ghztomash/callisto-module/firmware/drum-synth/AudioSampleCclap.cpp

// Audio data converted from WAV file by wav2sketch

#include "AudioSampleCclap.h"

// Converted from cclap.wav, using 44100 Hz, 16 bit PCM encoding
const unsigned int AudioSampleCclap[8833] = {
0x810044E8,0x00000000,0x00000000,0x00000000,0x00000000,0x00000000,0x00000000,0x0000FFFF,
0xFFFEFFFF,0xFFF6FFFE,0x0069000E,0x02CA00FF,0x0DA0083B,0x0A0D0FD7,0x05D10537,0x05DA048E,
0xF759FCD4,0xF66FF671,0xF0BFF594,0xC32CE56E,0xCFE7B396,0xDFFFE4FB,0xCCBECF0B,0xC8C1CF38,
0xD81ED27F,0x039DF2EA,0x1CEF1B4C,0x2C9E1B59,0x5279362F,0x71856B8B,0x57C46E6F,0x24BE3C05,
0x1A42142B,0x0F2724F7,0xD678DE7E,0xC3BEC6D0,0xE34ECB49,0xAF9BE7E2,0xA4F7969C,0xCC65C53A,
0xBEFEC7BB,0xB5B2AECB,0x0A7DD034,0x49E424F3,0x3CA65B39,0x721D45F5,0x7FFF7D3C,0x771B7FE0,
0x60FC66C9,0x3D735072,0xF5ED191B,0xD8B1E832,0x99A3B6CB,0x824A938E,0x884F8643,0xAC258784,
0x1354DF76,0xEA980F6E,0xDB5BEC39,0xF09FDA6F,0x04E30404,0xED0BF010,0xD35FDD2D,0x8E3899D1,
0xCF1AA1AD,0x2CB2FA63,0x579239BD,0x779F6F91,0x779F7BAB,0x603E6209,0x708771D2,0x3269599A,
0x43DB2C33,0x1F203123,0xD4B5F6FE,0xE397CC56,0xEEB0FC32,0xB519E76B,0x83D28D06,0x98E08B1D,
0xB228A036,0xC3EFBC7F,0x6CE41AC3,0x7A7C7D0A,0x09FA5221,0xC685DFB9,0xC8E8C79D,0x00CBD7E2,
0x314D371C,0xC418FA05,0x98859688,0x8F7292BB,0xA3498A4E,0xF5A3D082,0x0FC420BC,0x296F1A9F,
0x35BB1FC1,0x726E5D1C,0x5F417850,0xE385F978,0x2322128F,0xB9A50ABA,0xBD04AD18,0xFEF7C970,
0x66D64046,0x5C1A5F9D,0x10343BD2,0xF836FB74,0x14250467,0xFAAF0E3B,0x37870A34,0x2FB645A2,
0xF83C0BA6,0xC1B9E14E,0x912AA6BB,0xB2389C78,0x0429E052,0x347D1C0C,0x14442C00,0xEC55FBB0,
0xD577DDB8,0x21EAF607,0x49154262,0xF5A024CC,0xC550D4A6,0x081FDFD2,0x1FE5219C,0x0FC516D3,
0x050A03A3,0xF4DBF6CD,0xEF0FF3B7,0xD33CDD32,0xB074D06F,0xD1DAB9BE,0x0837F3A1,0x233512AF,
0x18752015,0x295B199A,0x3EB33078,0x23AE371D,0x25792089,0x3277330D,0x438F3A59,0x2C192ECB,
0x0DC620F9,0xECB1F9A2,0xD0A1D5FD,0xC890C527,0xC8FEC7EF,0xCC6CC572,0xD631D424,0xC9EBCB5A,
0xBA59C24E,0xDA3BC264,0x1508FAEF,0x2AD926C7,0x1CDD2624,0x143E15CE,0x36A82A17,0x2D293657,
0x08E11631,0x1E4B026E,0x37B42EE8,0x2C41390B,0x02471C53,0xC90BE561,0xC315C29B,0xC620C175,
0xD1B1CAAF,0xD10ED0D6,0xD7A8CE50,0xEE88E2D5,0x0964F93F,0x1D5809E4,0x28D42CB9,0x0A061E0F,
0xFC99FF52,0x16330BD6,0x16310FAE,0x2BBD2AF2,0x08FC1E9E,0x0473FAFF,0x13AA0839,0x076214DB,
0xF09904FC,0xFDF5ED66,0x035B0689,0xE42FF524,0xEA97E5D6,0xF30BECD8,0xDF28E859,0xCE33D09D,
0xF35EDF28,0xF350F637,0xF091ECD6,0x369D0C75,0x50154DE8,0x4B544FC5,0x373A447C,0x1009242E,
0xF885FB56,0xF148E8E7,0x14E40C26,0x05A70D7A,0xDDA0F808,0xE95EE2DE,0xF9C3EBCE,0x06D9F9A8,
0x08BA0811,0xE8FBF9BF,0xD0A5E076,0xC721C529,0xC7BCC7F3,0xDCA8D08A,0xEC42DF05,0x14D5FFEF,
0x541932B2,0x611E6013,0x4FD85A73,0x2C68341D,0x1FDF2C0F,0xFCC41398,0xF0D8E8D7,0xEE64F05E,
0xC78DDDEC,0xC48AB9B3,0xDA89D4F1,0xF3D3EB43,0xFA14F386,0xDEDBF36D,0xD0F8D6E1,0xDAFBDD31,
0xDCB7E2B0,0xE3FBD652,0x1487FA4F,0x448C33D8,0x2EDE3FBA,0xDCE105F2,0xE206CE4C,0x0568F6B7,
0x04A00E81,0x101B0ADC,0xFEF50648,0xF2BFF1EE,0xEFC4F125,0x11C601BC,0x35EC2890,0x709D4EAF,
0x7D33792F,0x7CF27E46,0x7BE77CD8,0x83FBDE75,0x026982E6,0x877D3CA7,0x865884C0,0x86D883EC,
0x86D08426,0x86A08AB8,0x9512934A,0xEED9A2A3,0x7A983627,0x7B057922,0x7AD87880,0x51266F11,
0x7BF26D04,0x21366A96,0x7A4673C1,0x79A577B6,0x527C6F1E,0x0B94FF2E,0xBD6AFEA8,0x435AC142,
0x76DA7A4A,0x76B97A69,0x76C37A6A,0x77177A61,0x761679A7,0x896BC234,0xB1E0AD79,0x93D8A700,
0xC22AACA5,0xAA9DB955,0x783A1D48,0x782377E4,0x76E97811,0x772F7871,0x76C8790C,0x764979AB,
0x304E7813,0xFD83CDCA,0x72B820BA,0x75B979F5,0x352C6473,0x162C1AB4,0x97A4F855,0x05D19896,
0x59165D9D,0xA227D25D,0xA0A6AB4E,0x5DADF549,0x78787742,0x152854C8,0x748A37A3,0x789975D4,
0x049752BD,0x78E953CA,0x78A676A6,0x785776EF,0x77A4771F,0x43B54977,0x176D382E,0x368F1D00,
0x10FE2135,0x69DF4CD0,0x38AB60C5,0x720755DE,0x77DF7648,0x776C7768,0x771777CA,0x540C7842,
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
};
