ghztomash/callisto-module/firmware/drum-synth/AudioSampleChat1.cpp

// Audio data converted from WAV file by wav2sketch

#include "AudioSampleChat1.h"

// Converted from chat1.wav, using 44100 Hz, 16 bit PCM encoding
const unsigned int AudioSampleChat1[8833] = {
0x810044E8,0xFFFF0001,0xFFFF0001,0x00000001,0x0003FFFF,0x0008FFFB,0x0027FFF5,0x0062FFB7,
0xFFBDFFCE,0xFFA5FD3F,0xFF720575,0x08D70556,0x07380674,0xE300F971,0x11CCF55C,0x06251241,
0xE1F1E32E,0xFC97F3D8,0x229821B8,0xF5462300,0xFBC0D2EC,0x07EFEC0A,0x06FB2626,0x2D90FCB6,
0x23671DFC,0xBE81FB95,0x1430DDD1,0x34F345A2,0xC65BFF5D,0xE6ACC791,0x3E69270B,0xE470FA6D,
0xD8E7FE9D,0x19F7F01F,0x0B0D3184,0x0FBA0278,0xE1FEF3AF,0xD878B7A9,0xDD4DB2AA,0x1A35155B,
0x03E83A13,0xDE0FE2AC,0xF6FAD71A,0x05102248,0x0DD80C1A,0x1F6B0799,0xE94CEADA,0x1B5D3042,
0xE1BF3894,0xE7A3A7C7,0x33D40931,0xEA0123C3,0xFC33D661,0x3B4913E5,0x42491FA0,0xCAFD1BBB,
0xECFC9ED2,0x561453B0,0xD69A35E8,0x02AED1FC,0xC7B3EF15,0x2332FE34,0x52B83019,0x8000F806,
0xD3889F14,0x485C4E74,0x8652A158,0x68672B6A,0xE12CB768,0x303A353D,0xAE0BE3DE,0xEEE3B3DB,
0x1BA5292D,0xF2A32134,0x4B7BE69C,0x22FB625E,0xA556EBFE,0x46A405EB,0xB1CDC5BA,0x6D863567,
0xCC6B1BC9,0x4B37E680,0xF778203B,0xCC691366,0xEF65B92B,0x4EC23A66,0xD70E25E8,0xBB7C8F34,
0x74B63526,0xD2963E80,0x16A5C713,0xB2C1F623,0x06CDD588,0xE46F0BE1,0x0E951A26,0xB4D5D1AA,
0x5CECE460,0x1E295F95,0xA1CADD4D,0xFA38A316,0x3EB72C01,0xD9AE19AC,0xECDCCDC3,0x18BBE9F8,
0x238174F4,0xDF4BF2C4,0xD11BB640,0xC772B9C1,0x517EFD3A,0xF3E1465F,0x7A7542D2,0xE1F24E08,
0x5566D9DE,0xCB0B3C55,0x00BDD283,0x2CFE47DF,0x38F8F11C,0xC4DF164B,0xD4DBA485,0x150C42E1,
0x3D3DFAA6,0xB8ECF167,0x2F210C8C,0x88D0C2F6,0xB0D78D03,0x113D215F,0x0423D4FD,0x4BE0651E,
0xB9D6C4E8,0xE54EF50E,0xE2FEDB09,0x7A6D47E1,0xF36C2BC4,0xE511C18C,0xFC62F3B9,0x399A0FDD,
0xF98E5C02,0x0F76AC7B,0xE36941C0,0x15582376,0x231928E0,0xD7A39B68,0xFDD019CA,0xE854C6F5,
0x7CB07015,0xD9246052,0xE3CACA41,0xEFAAD73E,0x0D2EC305,0xFED14BB7,0xF881B88A,0xE1F9FE28,
0xECB43570,0xE450A23A,0x63E235A4,0xEBF5289E,0x285625F4,0xACDBD9B8,0x3982EF85,0xF78E128B,
0x5EAD5763,0x8955D929,0x729AF7FB,0xDECE2D07,0x852D9AB9,0x31F3DC5A,0xE85AF624,0x3B6E4EF0,
0x027DC710,0x3BE964BA,0xAC1DC8E6,0xE35F1441,0x216BB24B,0x461365F6,0xF66209D1,0x819CA5DA,
0x2D83A71C,0xED4B695A,0x4511DB67,0x395F72C7,0xC39CA245,0x8AA9A712,0x3C4A0A67,0xEBC443FA,
0x08969EEC,0x93DF1C1C,0x5E80B239,0x1C757451,0x96F2BC85,0xAB999675,0x6188FAB4,0xD5F35173,
0xEBA1E1A3,0x0192BC4C,0xA896F528,0x613602D7,0x1E5544F2,0xCE000784,0x3A3CD6BC,0xB89127EF,
0x541EB371,0xFBC072B8,0x261CF0E1,0x134E52CA,0x2964C96E,0x36A06CC4,0xDAF99C00,0x46006693,
0xEE2A24A1,0x36F7F9ED,0x9ABCF2D8,0x5771DA3D,0xB18A6286,0x14A98D88,0xC2301ADA,0x38FDAEB4,
0x1BF27F37,0xB2A98A45,0x5EE944E9,0x97F8C35F,0x65D43C2D,0x8884E77A,0xDAA7B895,0x13ADD4B2,
0x2A866C76,0xCA9EA3E5,0x554A3B78,0xA057DA8C,0xF925DB9B,0x0CD3E8E8,0xDEF6119E,0xD3F5B7DF,
0xE7041A81,0x0041EC07,0x260DD9AD,0xE97D3279,0xD1FCE63C,0x6C1EED73,0xCE385F43,0xE9C2ABCB,
0x4FAE4062,0x9D55E147,0x0A0DF2DF,0x34581FA2,0x4BC0EBDA,0xD0914082,0xFE32A5CF,0xE1756B9B,
0x3469D172,0x17535969,0xD4DEB4E1,0x0E920595,0x1F20D896,0x01DC6997,0xDF548881,0x0690411A,
0x2D7B2FEC,0xE8FA267A,0x2375BE65,0x0C734A30,0xDBB9A8CF,0x78616173,0xC07A1840,0x113CF626,
0x92B8D2AC,0x2E52E95F,0xCDEFE0FC,0x5AD1232E,0xD80E3A38,0x2778E659,0x9F27ED46,0x661EC7E5,
0x11D8550C,0xA9AAC936,0x10100E23,0x36B5F1C5,0xB3FC251C,0x1923BCCA,0x36F96B14,0xC726C6E6,
0x1E82FB71,0xF9D4F942,0xC9DC1E82,0xFE239DD7,0x1BAEFB03,0xEC3A4A67,0x0E65EF10,0xFFA31024,
0xE6280BB8,0xC7FC8C08,0xFCDE1E9E,0x17F6C5A3,0xF92967CA,0x9C0B9640,0x4D93F37E,0x5B54610B,
0xDD6E1E30,0xB58D991D,0xD027F6C0,0x2E240F08,0x3A7F37E7,0xCB5DFB79,0x2863D308,0x5BC14FE7,
0xE2060CB5,0xB03FEFD9,0x2513F932,0x239FFF28,0x372D3B9F,0x3EF1236D,0xED892681,0xEF07EB08,
0xB06BC64B,0x700339E2,0x254E2C6C,0xAA211B05,0xECB69373,0xEF401C85,0x115EC393,0x5C1A7156,
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
};
