ghztomash/callisto-module/firmware/drum-synth/AudioSampleChat2.cpp

// Audio data converted from WAV file by wav2sketch

#include "AudioSampleChat2.h"

// Converted from chat2.wav, using 44100 Hz, 16 bit PCM encoding
const unsigned int AudioSampleChat2[8833] = {
0x810044DA,0x00000000,0x00000000,0x00000000,0x00000000,0x00000000,0x00000000,0x00000000,
0x00000000,0x00000000,0x00000000,0xFFFF0001,0x00050002,0x00100006,0x00220059,0x00ED0057,
0x01EF0091,0xFAA9FF7D,0x0094FB24,0x07D207D7,0xFA69024E,0xF78FF5BA,0x01F7FD11,0x04830091,
0x00C30913,0xFD7EFB93,0x0381049C,0xF6C4F9C5,0x076DFEDB,0xFD65FEDC,0x06CAFC9F,0x0B520898,
0xFC34069F,0xED0BEEDD,0xF948FC9D,0xF638F476,0x08990B49,0xFB3CF514,0x200E1160,0xF24C0437,
0xF6FAF004,0xE358E483,0x14DC07D4,0x03851799,0x04B40FDD,0x034004ED,0xDDACF804,0x0787D2AA,
0x195A27F8,0x08AC0DD5,0x0A9718DE,0xEF78FAD1,0x1EAF0708,0xECF21BBD,0xD42AB687,0x0DD61B6D,
0x3F3F33B4,0xE7F40341,0x4176F732,0x2E9F36E1,0xD93D1332,0x42BFF911,0x13835575,0x96E8AF25,
0xC6518C13,0x35052F3E,0xED681CDB,0x07CEBBA1,0x020447CD,0xFC150612,0xBE04D7C0,0x4811F3F7,
0x2D0FDE77,0x16B47BC0,0x9E72C6EC,0x2083E67A,0x16185311,0x880086CB,0x3DB2CBEE,0x7C347C2B,
0xCE284C38,0xB758940A,0x47F0E5ED,0xD47B5DD7,0x78E91F9A,0x892FD430,0x80008973,0x7337D9C6,
0x64B57C9A,0x839EB048,0x254CC562,0x161D1CD5,0xB9E1BBB9,0x8B52F273,0x6E86B47F,0xC5E46071,
0x8F6788A0,0x2D4ED543,0x5D2F72BC,0x8E7BEAAC,0x1191C1EE,0xEFBF019C,0x7872586C,0x452A60B6,
0xFE323323,0x21D2F10A,0x9BE34C68,0x397D97E2,0x618A2CC8,0x002C669D,0x35BA201E,0xF5B31BB4,
0xF723FED3,0xA18893FA,0xCFAB11E5,0x75484C71,0xE68B6D22,0x05058B5C,0x01AE1595,0x61D9F1E4,
0x979F372C,0x002FCF73,0xC1002A7E,0x25AAFA92,0x30ECF9A6,0xAE4E04AC,0x98B48CA3,0x76204297,
0x99550C08,0x65DD287C,0xC96B2D0C,0x66F94C4C,0x8E6DC963,0x6A67B50B,0x5FA26B6C,0xC3CAEBB8,
0xA23EA019,0xC466BB11,0x601523DD,0xC9E74289,0x1C68AF81,0xACFF0304,0xAAE1A3E8,0x969EB306,
0x6E3B11D8,0x71106C91,0x9CD52487,0x2209C147,0x1C57517D,0xC8D4D243,0x2CFB0055,0xEF1817EF,
0xBAFCDF22,0x1579BF4E,0x2A7836E6,0x09600079,0x8BEEC7B8,0x63C9BBAB,0x63217519,0x8C13B447,
0x465DC9E1,0xFECE50CA,0xFBDA1785,0x0D6EC943,0xCF4ED688,0x959DB4A5,0x91A7942C,0x6CF4152D,
0xB4EE4060,0x6C10DDDC,0x612B4A0E,0xD479267E,0x14D00B2F,0xCED0D90E,0xE6F5D26B,0x38FA0A45,
0xF167424E,0x191831FA,0xC2C9B143,0x509D1A24,0xDE4A21CC,0x945D9938,0x6C32F467,0xCB8C6511,
0xA1868EA1,0x70EF3467,0xD57E6626,0x402DD686,0x67A7517F,0x671769A0,0xB860DE4E,0x6E3A677B,
0x54AD6A8E,0x15166989,0x3294DEEA,0x5DEE5589,0x5449604D,0x92A8DD45,0x544ED843,0x57526BC3,
0x6C286D2A,0x5B9D6350,0xA1ABFB26,0xF798987C,0x6C596C8A,0x65EF6CDC,0x43226D09,0x06B50517,
0xE2B4AFD1,0x3FA85DE5,0x1B5E2B18,0xBCBDFC0E,0x440CB94D,0xD12227C6,0x3C23BCED,0x588B6C2B,
0xC99D5CC6,0xE355948A,0x6DFE61EC,0x453E6B3C,0x0D95EDFE,0x0CCF0DEA,0x6F594C16,0x50416996,
0x989114D1,0xC1AE8FBF,0x6DCD5C00,0x4D704822,0xC6A9FAF6,0x608C4240,0x30BF5E90,0xACDCC796,
0x964EC58B,0x549EB3D7,0x13C36CF8,0x64C7D137,0x1A0B6A24,0x9244E157,0x5855B6ED,0x695A6D41,
0x02086CE8,0xC561A77D,0x2BFC6D19,0x5741CD72,0x10F20A5B,0x24032DEF,0xD6A905F8,0x286DE79D,
0x6DF966ED,0xD32035DF,0x54B411F3,0xF2FB40D9,0xEDE04788,0xD68D93B5,0x6219337B,0xF579168A,
0x34D300D8,0xF3E3206C,0x93A8C486,0x4E63C7DD,0xEE2753A4,0x6557E355,0x1A5518E3,0xD2906584,
0x5D2009C4,0xDA2F2C45,0x5A41D841,0x2F44509B,0xA1082EF2,0x6B4EEEA7,0x5FFE6C06,0xAF87DA3A,
0xADD2D45C,0x01A49575,0x65C36BA1,0x9821B0FA,0x47CC31C7,0x413756E6,0x60246B31,0x204E1279,
0x30892D06,0xB1D4B663,0x476F0AAC,0xEA0B9892,0x098A6C93,0xDA41FF22,0x690D18E0,0x95AF145C,
0x2E38A3A6,0x67FD6B39,0x60FE5B17,0xBF3760CA,0x47949C8D,0x634B6EBC,0xB897CFCE,0xFD54A618,
0x2D696E37,0x1D6CCDF5,0x1BB3423C,0xE1B8B60F,0x1F853F69,0xEBA59A88,0x36BA692F,0xACF0DACE,
0x078A4AAF,0x43542427,0x302FC04A,0xF55169D5,0xFB9EEE29,0x5652E033,0x984725C3,0x049E9A55,
0x570D6B76,0x632167D8,0xA092ACE0,0xE161ACD3,0x0AC9FA2C,0x5D6130B7,0x34465D5F,0x5CA9359C,
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
};
