ghztomash/callisto-module/firmware/drum-synth/AudioSampleCkick.cpp

// Audio data converted from WAV file by wav2sketch

#include "AudioSampleCkick.h"

// Converted from ckick.wav, using 44100 Hz, 16 bit PCM encoding
const unsigned int AudioSampleCkick[13249] = {
0x8100675C,0x000800BD,0x08BD039F,0x0F000C42,0x141E1187,0x15711595,0x16AB15FE,0x1448156E,
0x14DF13B8,0x18BD1776,0x19E818F8,0x225F1B40,0x39482D2E,0x4CD543CC,0x61B9576D,0x75966C75,
0x7D9A7B44,0x7F057EA5,0x7F4C7F38,0x7F067F39,0x7E687EBD,0x7DA37E08,0x7CD37D3A,0x7C0C7C6D,
0x7B587BAF,0x7AB97B04,0x7A307A71,0x793479EE,0x78237885,0x7639778A,0x6F06736A,0x64A869FA,
0x57235DED,0x4AA1517C,0x3B094326,0x2A4A3313,0x16A31FD3,0x02B70D48,0xEB90F739,0xD86AE18B,
0xCA54D092,0xBDB7C3EB,0xACB1B64C,0x9ED6A478,0x96489A43,0x8DF191F6,0x89838B08,0x882788AB,
0x87E487F2,0x886E882C,0x88E188AA,0x893E8911,0x89898965,0x89C689A9,0x89F789DF,0x8A208A0C,
0x8A448A33,0x8A638A54,0x8A7E8A71,0x8A968A8A,0x8AAB8AA1,0x8ABF8AB5,0x8AD08AC8,0x8AE08AD8,
0x8AEF8AE8,0x8AFC8AF5,0x8B088B02,0x8B138B0E,0x8B1D8B18,0x8B278B22,0x8B308B2B,0x8B388B34,
0x8B3F8B3B,0x8B478B42,0x8B4E8B48,0x8D478BBE,0x93288FC2,0x9C7A975D,0xAAC1A2E0,0xBE86B457,
0xD6B4CA68,0xEC8CE215,0x01A8F76F,0x172F0B9F,0x2F0B230D,0x462E3B47,0x59084FCC,0x672460E7,
0x6ECC6BB4,0x7346716A,0x74B47448,0x74B974BD,0x74B174B5,0x74A974AD,0x74A274A6,0x749C749F,
0x74967499,0x74907493,0x748B748E,0x74867489,0x74827484,0x747E7480,0x747A747C,0x74777479,
0x74747475,0x74717472,0x746E746F,0x746C746D,0x7469746B,0x74677468,0x74657466,0x74647465,
0x74627463,0x74617462,0x74607460,0x745F745F,0x745E745E,0x745D745D,0x745C745D,0x745C745C,
0x745B745B,0x745B745B,0x745B745B,0x745A745B,0x745A745A,0x745A745A,0x745A745B,0x745A745B,
0x745A745B,0x745B745C,0x745B745D,0x7435745D,0x70C8730E,0x696B6D97,0x5C57637B,0x4A905406,
0x35C8403F,0x22912C75,0x0E101828,0xF95C041F,0xE381EDE4,0xD14DDA28,0xBC35C6A1,0xAD42B415,
0xA004A666,0x967E9AAC,0x900492CC,0x8CA98E11,0x8BAB8BE9,0x8BC48BB8,0x8BDE8BD3,0x8BF68BEB,
0x8C0A8C00,0x8C1D8C14,0x8C2E8C25,0x8C3D8C36,0x8C4B8C44,0x8C588C52,0x8C648C5E,0x8C6E8C69,
0x8C788C73,0x8C818C7D,0x8C8A8C86,0x8C928C8E,0x8C998C95,0x8C9F8C9C,0x8CA68CA3,0x8CAB8CA8,
0x8CB18CAE,0x8CB58CB3,0x8CBA8CB8,0x8CBE8CBC,0x8CC28CC0,0x8CC58CC4,0x8CC98CC7,0x8CCC8CCA,
0x8CCE8CCD,0x8CD18CD0,0x8CD38CD2,0x8CD58CD4,0x8CD78CD6,0x8CD98CD8,0x8CDA8CDA,0x8CDC8CDB,
0x8CDD8CDC,0x8CDE8CDD,0x8CDF8CDE,0x8D1E8CDF,0x8F848E02,0x94E591C1,0x9D4298E0,0xA858A23E,
0xB65AAEF9,0xC698BE42,0xD894CF7D,0xEC0BE244,0x0144F6C5,0x15410B89,0x27851E5B,0x36562F3B,
0x44213D40,0x51BE4B16,0x5BD4579C,0x64195FF4,0x6A4C678B,0x6EA56C81,0x71EF709D,0x731672AD,
0x73467344,0x73447344,0x73437343,0x73417342,0x73407341,0x733F7340,0x733E733F,0x733E733E,
0x733D733E,0x733D733D,0x733D733D,0x733C733D,0x733C733C,0x733C733C,0x733C733C,0x733D733D,
0x733D733D,0x733D733D,0x733E733D,0x733E733E,0x733F733E,0x733F733F,0x73407340,0x73417340,
0x73427341,0x73427342,0x73437343,0x73447344,0x73457345,0x73467346,0x73477347,0x73497348,
0x734A7349,0x734B734A,0x734C734C,0x734D734D,0x734F734E,0x7350734F,0x73517351,0x73537352,
0x73547354,0x73567355,0x73577357,0x73537359,0x72AF7327,0x708571BC,0x6CF76F03,0x673D6A43,
0x5FD363D1,0x57745BCE,0x4C6C523E,0x3DA045B4,0x2CF73526,0x1C4A24D8,0x099B1328,0xF617FFE0,
0xE3CAEC5E,0xD3EEDBEF,0xC3E0CBDA,0xB5FABCA2,0xAABEB021,0xA137A58E,0x991C9D0D,0x92D29594,
0x8F2590C2,0x8D3F8E06,0x8C9B8CC3,0x8CAC8CA3,0x8CBD8CB5,0x8CCD8CC5,0x8CDC8CD5,0x8CE98CE2,
0x8CF58CEF,0x8D008CFB,0x8D0B8D05,0x8D148D0F,0x8D1D8D18,0x8D258D21,0x8D2C8D28,0x8D338D30,
0x8D398D36,0x8D3F8D3C,0x8D458D42,0x8D4A8D47,0x8D4E8D4C,0x8D528D50,0x8D568D54,0x8D5A8D58,
0x8D5D8D5C,0x8D608D5F,0x8D638D62,0x8D668D65,0x8D688D67,0x8D6A8D69,0x8D6C8D6B,0x8D6E8D6D,
0x8D6F8D6F,0x8D718D70,0x8D728D71,0x8D738D73,0x8D748D74,0x8D758D74,0x8D758D75,0x8D768D76,
0x8D768D76,0x8D778D77,0x8D778D77,0x8D778D77,0x8D778D77,0x8D778D77,0x8D778D77,0x8D768D77,
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
};
