ghztomash/callisto-module/firmware/drum-synth/AudioSampleCsnare.cpp

// Audio data converted from WAV file by wav2sketch

#include "AudioSampleCsnare.h"

// Converted from csnare.wav, using 44100 Hz, 16 bit PCM encoding
const unsigned int AudioSampleCsnare[8833] = {
0x810044E8,0xF5ADF66B,0xF4C5F500,0xF5EBF451,0xFE8BF8FA,0x18CF0A17,0x3C2D2AEA,0x5B094BE9,
0x6F736771,0x72BA72DA,0x6C4C6FFD,0x6452682E,0x5D3E60B0,0x568C59C1,0x50A15397,0x4A464DF1,
0x43934731,0x37893DED,0x2BDC31CB,0x229B26B4,0x1B981F4E,0x142617A9,0x0CDF1060,0x05170910,
0xFD58013A,0xF5D5F977,0xEF19F2A5,0xE893EBB1,0xE310E5BC,0xDD00E00A,0xD7CCDA2A,0xD2A3D558,
0xCE7AD06D,0xCADACCC8,0xC6EFC8A0,0xC476C527,0xC27DC3AA,0xB63BBF07,0x95BFAC86,0x8000830D,
0x811C8031,0x828681B1,0x83E9832B,0x85288485,0x863F85B5,0x872D86BA,0x87F68795,0x88CE884E,
0x8B3E89CA,0x8F8A8D27,0x9580925D,0x9CC69900,0xA4DBA0A2,0xAEBAA9B4,0xB97DB3FF,0xC52BBF25,
0xD1F1CB5A,0xE167D7F9,0xE69DE995,0x2D2AFA94,0x62374F33,0x74006F22,0x761C762D,0x75D97693,
0x74B47660,0x72B17567,0x729F754E,0x615372B3,0x39D75827,0x8892A429,0x91218B5A,0xBC47A9C5,
0xD6B4CCD8,0xEACEE258,0xFA65F3B4,0x062A0118,0x0F030C2C,0x124B109A,0x1A1A17CE,0x1D431B47,
0x23D92002,0x29AB25BB,0x2BF12AA5,0x343F2D78,0x43D63BC0,0x6D46654B,0x38815566,0x2DA82E23,
0x370D3101,0x3F473AE8,0x449C4127,0x48BE4573,0x4C0A48C2,0x58FA4B3B,0x5D6872C4,0x76457446,
0x7552747A,0x75CB740E,0x759674AE,0x756774D8,0x754074F4,0x75247504,0x75127508,0x74FA7504,
0x73F874AC,0x70B172B1,0x6A176DD2,0x5FF7657C,0x5253598F,0x41B04A55,0x2EE5387F,0x1AD424FA,
0x0646108E,0xF20AFC10,0xDED4E847,0xCD0FD5B9,0xBD23C4DF,0xAF70B5F7,0xA440A984,0x9B669F8B,
0x94C997D3,0x903D9246,0x8D948EB2,0x8C6F8CD5,0x8C7D8C60,0x8C9E8C92,0x8CAB8CA6,0x8CA38CB0,
0x8C9E8C96,0x8CB08CA8,0x8CC08CB9,0x8CD48CCA,0x8CEB8CE0,0x8CEE8CF5,0x8CE28CF4,0x8CCB8CFC,
0x8CA68D0A,0x8C718D30,0x8C2D8D6F,0x8BD28DB5,0x8B958E04,0x8BD78E65,0xCBC58FA6,0xA7F1B395,
0x8BDB8F31,0x8C218EA7,0x8C8C8E55,0x8D068E16,0x8D9E8DFD,0x8E028DF5,0x8E558DC6,0x8EA98D95,
0x8EF08D62,0x8F208D34,0x8F478D24,0x911A9093,0x7014460C,0x8F85D32A,0x8F5F8EC6,0x8F248EE6,
0x8F3A8EFB,0x94F29163,0xA0769A97,0xB08AA81E,0xCB18B5F4,0xD02AD13E,0xDB05D308,0xEE40E3E5,
0xFF25F530,0x0F2B044A,0x2F14128D,0x40354C1A,0x751E6AB6,0xEF785B2E,0x9C7F9233,0xDD88E740,
0x719F601B,0x733F46D8,0x9C5C39AC,0x99198DFE,0xD83AB864,0xE7D8E015,0xF39AEB53,0xFE89F880,
0x05620197,0x0A9B07CD,0x0ED70CAF,0x125010A2,0x154913CB,0x17FC16AB,0x1A58192D,0x1CC11B87,
0x1EAB1DA5,0x20921F74,0x2246213D,0x23C422C5,0x34652960,0x587144DC,0x70276E72,0x58686D54,
0x26A231D2,0x26742CEC,0xEE4B0EA9,0xE3F8DF53,0xFB46F028,0x0937032D,0x0F070E12,0x043D09F4,
0x01820187,0x03B60233,0x04240596,0x24B91420,0x04F91C16,0xE72BF09D,0xF0FCE72C,0x079AED5E,
0x19FA313C,0xD27FED4D,0xD3B3D05C,0xE83EE21B,0x4443EE9F,0x0FF64AF2,0xB031CCCC,0xB8F6B1A1,
0xC23DC02A,0xC264C29F,0xCE89C17D,0x0BCDE13A,0x700F6543,0x65C0702D,0x56215F54,0xEE051ACF,
0x64FC04B9,0x628C6E30,0x59A85A97,0x5AB35D80,0x52D7586E,0x465C4DBB,0x36583F2D,0x23042D3D,
0x0DAF18A9,0xF71B0285,0xE143EC0D,0xCCEBD6D7,0xBABAC35F,0xAC15B314,0xA08AA5F1,0x98649C07,
0x92FE955F,0x905A9146,0x9027902A,0x900A901A,0x90269008,0x908B9061,0x909E9092,0x9081909E,
0x9089907F,0x90989086,0x90429098,0x9030900C,0x9008902C,0x900F8FFA,0x90349040,0x90269011,
0x8FE29025,0x8F798F97,0x8F918F81,0x8FAA8F9A,0x8FE18FCD,0x8F9A8FCF,0x8F768F79,0x8F7A8F73,
0x8F968F85,0x8F7C8F8F,0x8F9F8F84,0x8FAF8FB2,0x8FE68FBE,0x8FE98FF2,0x8FBB8FEC,0x8F9B8F8C,
0x8F998F96,0x8FBE8FB4,0x8FD28FCF,0x8FBD8FB9,0x8F2C8F7F,0x8F8B8F62,0x8F898F85,0x8F4D8F67,
0x8F678F54,0x8F708F75,0x8F4E8F5F,0x8F428F4A,0x8F408F34,0x8F698F5B,0x8F698F6C,0x8F4B8F5C,
0x8F868F60,0x8FF68FCA,0x90B98FD7,0x97029324,0xA2BA9C40,0xB30FAA64,0xC60ABC63,0xDA85D01B,
0xEFA7E4EC,0x04BBFA6C,0x18A70ECD,0x2A6421DD,0x3A663285,0x48AE41D0,0x54884EF8,0x5DB0596B,
0x64BF616F,0x6A1967A4,0x6DB86C26,0x6F796EC0,0x70357001,0x7064704A,0x703C704C,0x7035704B,
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
};
