ghztomash/callisto-module/firmware/drum-synth/AudioSampleClap1.cpp

// Audio data converted from WAV file by wav2sketch

#include "AudioSampleClap1.h"

// Converted from Clap1.wav, using 44100 Hz, 16 bit PCM encoding
const unsigned int AudioSampleClap1[8065] = {
0x81003E88,0x00000000,0x00000000,0x00000000,0xFFFD0000,0x00A60008,0x020201AF,0x00E001AC,
0x016B011D,0x01260121,0x0014FFD3,0xFFEAFFEF,0xFF5DFFFF,0xF954FD06,0xFDD2FACF,0xFB6CFC95,
0xFB77FB29,0xF98DFAAB,0xFA7CFAC2,0xFD18FCF5,0xFE49FF0E,0x0197FFD9,0x076A02E5,0x09FE09A0,
0x076209B7,0x05210626,0x065A049D,0x022705F1,0x00CFFF81,0xFDA3FD11,0x00B5FEA4,0xF5DEFC92,
0xFA32F768,0xF883FA3B,0xF634F825,0xF5ADF35C,0xFD4DF83F,0x0439FE46,0xFE9601B5,0x0C900666,
0x11940CA5,0x0DE60EF7,0x0F760DA5,0x0BB30CCA,0x06470787,0x02B405E4,0xFB0AFE0E,0xF1E9F827,
0xEFF7F5AA,0xF8E1F0FA,0xFD5CFA12,0xF9A0F9DB,0xF80CFC06,0xFDFDFA72,0xFDC9FE0A,0xFEA8FC55,
0xF8E5FBCC,0xF1DDEDE5,0xF7E2F374,0xFF11F9E3,0x0612FE37,0x0D9A0962,0x0DAF0E80,0x117809F6,
0x10D113EB,0x0AD30B66,0x0EB80DA5,0x0912095C,0xFFDE0244,0x029100AE,0x010D02E8,0xF680006F,
0xF0A1F1B9,0xF20FF404,0xF4B7F3A1,0xF626F2D2,0x0CA904E3,0x0C7E1079,0x02D906FD,0xFD920104,
0xFB8DFDBA,0x0534FF4F,0x02C308B3,0xF8EEFE04,0xF5E5F3F8,0xED24EECB,0xF1B4EAB7,0xF89FF4B1,
0xF9DDFCDD,0xFFB10085,0x0440FDF8,0x10B10B04,0x0586113A,0x05A1FD37,0x05800926,0xF769FEA8,
0xF984FBF6,0x023AF9CD,0x0AE307E8,0x0AE40843,0x01F00471,0x00A90185,0x01DE019B,0xFF92FF42,
0x099C05ED,0x049506F4,0x0220022C,0xF926FDA4,0xF056F3A6,0xF76AF547,0xFE20FCB3,0x045F024F,
0x013F0264,0xFE4BFFE5,0xFBE2FB9F,0x04F0011E,0x044C06D7,0xFE7FFFB6,0xFA60FB5A,0x01B7FF52,
0x03030303,0x02980340,0x02B101EC,0x016D0006,0xFE95FFE4,0xFB43FC18,0xF353F821,0xF927F898,
0xFD5CFC9C,0x00B8FF95,0xFFD7FF47,0x0383019F,0x055D0352,0x035E037A,0x060C0434,0x07090689,
0x091508A8,0x09D10622,0x06E607CD,0x02DB0470,0xFF7CFEEE,0xFE1FFD5E,0xFAA1FB64,0xFA65F905,
0xFA38F9B3,0xFA4DF952,0xF869F838,0xFAD3F98D,0xFE45FC0F,0xFF8D000E,0xFF54FFCE,0x005BFF52,
0x03F30316,0x041903F0,0x039E038F,0x06510391,0x06FB063F,0x04AF063F,0x01F403AB,0xFDB7FF9F,
0xFBF4FD91,0xFAADFA1B,0xFB5CFA84,0xFA61FA94,0xFC60FA6D,0xFE21FC95,0xFF9DFF3A,0x01ECFF2D,
0x033302E3,0x003F0160,0x0032FFD4,0x002100DA,0xFF29FDFC,0x0076012C,0xFF31FFED,0xFE87FE87,
0x0038FE8B,0x01E300F8,0xFEDF01D7,0x018A0042,0xFF3C008F,0xFDCFFDE9,0xFEBFFF75,0x0007FF8D,
0xFFF3FFE4,0xFCC2FD46,0xFF5FFE0E,0x00AD0083,0xFFD6FFA1,0x00C40068,0x00710115,0x016D0126,
0x01E4018F,0x01CC01F6,0x0078018A,0xFF40FE8C,0xFFEC0023,0x001D0034,0xFFB4FFEF,0xFF06FEDA,
0x016D002D,0x023401C7,0x00B60190,0x01530124,0xFFE70165,0xFEBCFE9F,0xFE7AFEFF,0xFE3FFE2D,
0xFEDCFEEE,0x0029FEEA,0x01AE0108,0x017C01C7,0xFFE2003D,0xFFC3001A,0xFF3BFF7A,0xFDE4FE94,
0xFEA9FD67,0xFFA7FE83,0x00490015,0xFF54FF8A,0xFFA5FF68,0xFF730002,0xFF1AFF39,0x005AFFA0,
0x011E0120,0x013D0170,0x009A00EC,0x000A0066,0xFF55FF31,0xFF78FFD7,0xFE9EFF4A,0xFE81FECE,
0xFEE4FE26,0xFF11FEF2,0xFEC0FEB6,0xFFA5FF2F,0x00B50044,0x017200FC,0x021C01AE,0x037A030C,
0x03F7042E,0x03A103BF,0x43AD0D17,0x71437FFF,0x3B8764F9,0xFA4BEE89,0x2BB425C2,0xDCC81A17,
0xC459AB85,0xAF7BA841,0xD2C1BA8B,0xCBE2D44B,0xD410DBE3,0xEA49DED8,0x021BF09E,0x15611255,
0xFC4613DC,0xFAF70661,0x076A0AF3,0xF98FEEE4,0x09B20FAC,0x094A1330,0x006A00F3,0xFF59F86E,
0xE668F164,0x00D9EE7A,0x0605084B,0x07040FFB,0x0BE905DA,0x2E2A2525,0x06632AC9,0xFBCAECA2,
0xEC94F98D,0xE243E750,0xE210E92F,0xDFC5DBBD,0xFD74F61A,0x08BA0565,0xFA43F8CB,0x19ED0FF4,
0x24232BDC,0x1BCE1EB5,0x023E0D79,0x02DFFC7A,0x17AF01DE,0x05A016F2,0xFF9B051E,0xFC50FE94,
0xE02BEFFC,0xFB60ECE8,0xF769FE66,0xE88FE450,0xDBF2E34A,0xF6B2EFA8,0xF50EFE27,0xEF96EA81,
0x05E1FDE6,0x039A0339,0xF98BF71B,0x10870BA8,0x1A5F18FC,0x18F11836,0x11D416ED,0x0446020F,
0xFAD7FC3D,0xFBDFFEE7,0xF673F3A6,0xFC380106,0xF105F507,0x0036FE93,0x07C6023C,0x156A0D24,
0x16981D6F,0xFFA510A5,0xFCFFF922,0x09BE07E9,0xFB2A03F1,0xF14AF38D,0xF260EFC2,0xF575EB9E,
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
};
