ghztomash/callisto-module/firmware/drum-synth/AudioSampleHat1.cpp

// Audio data converted from WAV file by wav2sketch

#include "AudioSampleHat1.h"

// Converted from Hat1.wav, using 44100 Hz, 16 bit PCM encoding
const unsigned int AudioSampleHat1[3457] = {
0x81001AB1,0x00000000,0x00000000,0x00000000,0x00000000,0x00000000,0x00000000,0x00000000,
0xFFFF0000,0xFF64FFE4,0x0116FF5E,0x00190184,0xFFB8FF05,0x011001F6,0xFE78009A,0x01E0FED5,
0xFFBE024D,0xFE1BFE18,0xFFE4FEED,0x04BA0401,0xFA8AFD12,0x04A9FB1C,0x02E804BE,0xF80DFCB8,
0xFF27F968,0x05D403EF,0x093D08B5,0xF249FD4A,0x0303F405,0xF77005CF,0x03B1FB69,0x02DB0FCE,
0xF599FB2B,0x04F5FBE4,0xF32BF4B4,0x1D7D1526,0xF040FDF9,0x15D4F213,0x0B4709C6,0x127D0278,
0xDF68F437,0x0848DACE,0x0FCC1C02,0xEC900F4A,0xE3CDE987,0xF472ECD9,0x14990CE9,0xFF681233,
0xFD68FEA1,0x0B4C0E84,0xBD3FDB13,0x16A3DFE9,0xFE802A5B,0xE87AE620,0xF227F90C,0x0D2710B3,
0xF3D6D04B,0x27251211,0xE342EA76,0xF5C6FA68,0xECB7F908,0x1EBEFC8F,0xD81F074F,0x124A03D9,
0xF05CE667,0x079FDD67,0x191410B9,0xDF20ED80,0x074CF971,0x2BA8ED2E,0x0CE02FAB,0xE79EEEAE,
0x70E13710,0x13E0557B,0x8000ED95,0xE7918CF1,0x513F2B21,0x16ED4678,0xF94FF97E,0x234F1B09,
0xD61B070A,0xC0C0AB1D,0x06D6F290,0x2A012237,0xD852EBF5,0x71A907B2,0x16B84D1C,0xC933FC53,
0x1593E96A,0x4D0354A7,0x4F1649AF,0xE7201BC1,0xA5C9BEA3,0x245ED967,0xEFE12FA8,0xF96FC2B3,
0x23292B46,0xCE07EE0F,0x161BF124,0x259C1D01,0x0E8847E5,0x972AC9B2,0x42E5F0E0,0x30E651FF,
0x064F18F4,0xA289BF74,0xFA368FB9,0x55274C28,0xDD93F417,0x46D702DF,0xC92F0055,0xF15CB799,
0x1154D81E,0xF85F420F,0x1EC013CA,0x024E342D,0xDCE9D86E,0x12830C47,0x0F74F66F,0xD31AF153,
0x21EEF447,0xE9783664,0xC180E003,0x3BD0E3EB,0xA9EA176C,0xCF4F9ACE,0x03E72A86,0xECBCBC6B,
0x292C6C61,0x91F0A46C,0x66F9D9B5,0x568D4572,0x063BFB31,0x3FB00E67,0x21FA3581,0xF02E0A0C,
0x3153F83D,0xEBB41EA4,0x03F50153,0xB686F8F1,0x2D690DE3,0xD15FFEEF,0xD60AAC17,0xE38C0046,
0xDA19BB47,0x12BFEB08,0xEA7D373E,0xF6C4ED10,0xAF6CDF12,0xD16DB0A0,0x05050197,0x20513DC5,
0xD8C319B3,0xECD0D377,0xEAFF2797,0x105CE18C,0x36216425,0xE358E176,0x468A0260,0xE0E42102,
0x421DEDE3,0xC431355C,0x43D2A85E,0x3D176E1D,0xF4F538C7,0xEB191BD3,0xBDA9E1B0,0x316013C4,
0x0CF5424F,0xEB5A212B,0x1437075A,0xE4A0FE93,0xF489E132,0x3CB62ED9,0x105C1052,0x0F3A1E92,
0xC4C7C598,0x0FCF1AEF,0xDD000086,0xF2DFD06A,0x22AF066F,0x147329D6,0x0743CC56,0x19020E04,
0xE00110C7,0x1AE6CDCE,0x04CB1801,0x14CCFE8C,0xD55116D5,0x8F729152,0x3007EA90,0x2C813C08,
0xE681118F,0x02FECD03,0x0EEB009D,0xEB61EC1C,0xEAF6D379,0x37011370,0xD36206F7,0x0F160073,
0xBDBFA978,0x2B4ACDF7,0x2F8E5BBD,0xB492D7B5,0x45160034,0xE4190F83,0xD5F7C0AB,0x02443219,
0xD0C4B3A6,0x5B1C3016,0xF7B72B2A,0xB7F2E3D5,0xD693F69E,0x19B1DCFC,0x2F054CEA,0xF0392E57,
0xE565E9F4,0x11BC0699,0x1F6C1D0C,0xDCCEFB06,0x48A2167B,0xEBCC2E81,0x1643F06A,0xC192DA40,
0x1ECCB946,0x0CA90B41,0x464A1A97,0xDB110779,0x33314067,0xBFCB0290,0x2078E184,0x37B91BBF,
0x32D52103,0x05FE08A0,0x1866FFF6,0xD80FDE70,0x365B15B3,0x00E93255,0xE879EB08,0xCDF6E81A,
0xB5E2A3C9,0x24F2F6C7,0x161F1F1C,0xDF52D7A9,0x2144F75B,0xF6FC0B0F,0xEDADF1AD,0x21E0FD6A,
0xD894F812,0x349FDDF2,0x0F4651BA,0xD4CDC749,0xC55AFE49,0xD53ECBE1,0x19D4F30A,0xF788030E,
0x20BBF6B0,0xE76D0953,0x144A03A7,0xE72DA561,0x4B801AA6,0x14A64186,0x9584DDBA,0x06E1B884,
0x14CC24D2,0x2D110A3F,0x10303E6A,0x043EDA43,0x236F355E,0xDBC0FB63,0x12C90F8D,0xEA3AEBB9,
0x23E75FFA,0xF768106E,0xED67DA75,0xFA7DE8CD,0x1959FF60,0x122B07C0,0x2C86112F,0xFB631A5A,
0xFE62DCEB,0x06980139,0x07612035,0xD8C9EAA3,0x2949FA0B,0x0BBF29B4,0x06C8FC43,0x0FBCF23D,
0x11D01E58,0xF5A4F34D,0xD3140F62,0x20F9E960,0x06C3F462,0xD551003A,0xD1BEE102,0x0B1FC295,
0x1F2D3B5E,0xDA031005,0x0737DAFE,0xE635014C,0x03C80574,0xE70D03A3,0xF398C789,0x2B0339B5,
0xD680F219,0xD6BDD45B,0xED31BAED,0x4F04130B,0x31433DFA,0xB0CAD9BA,0x3E8306D1,0xF2A21CCD,
0x2ADEF46D,0x10F82495,0x12BF03DE,0xDEBCD8B1,0x05161208,0x1212228D,0xF90B11E8,0x28F0134A,
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
};
