ghztomash/callisto-module/firmware/drum-synth/AudioSampleHat2.cpp

// Audio data converted from WAV file by wav2sketch

#include "AudioSampleHat2.h"

// Converted from Hat2.wav, using 44100 Hz, 16 bit PCM encoding
const unsigned int AudioSampleHat2[12033] = {
0x81005DFD,0x00000000,0x00000000,0x00110002,0xFFF70017,0x0050002F,0x00B40077,0xFE47FEFF,
0x0117FF94,0x00FE0219,0xFE65FFCA,0xFF12FE3D,0xFFC2FFBB,0x01C6FFB9,0xFE8E0119,0x00E0FF6C,
0xFF5E0179,0xFF5CFD87,0x00E20133,0xFFC1FDF1,0x0240FF86,0x02F10164,0xFE100091,0xFEAAFC3A,
0xFBCE0033,0xFFF0FCD9,0xFCD70324,0x0220FB60,0x04090633,0xFEB2FC5B,0xFC6FFF32,0xFCADF674,
0x011A04A4,0xFECC0204,0xFEA0050C,0x006E03D3,0xF3F2FB74,0x07D0FAE1,0xFF25049A,0x03AD02EF,
0xFE2C0739,0xFDF9FDEB,0x091C086B,0xF2E2029A,0x01F6F0D8,0xFEBC04EC,0x06C912F0,0xFE96F793,
0x14BC080F,0x0CE8079F,0xF911FE46,0x1BCD0F94,0xFD36121A,0xEB3CEDEE,0x040FE84D,0x02D80CDB,
0xF303FFE2,0x1260F626,0xF8020882,0xFB800A97,0xF7B7F1E3,0x04730AFD,0x2AF0EE43,0xEE8E1E82,
0xF0EAF5ED,0x150D0C55,0xE5781B64,0xDE5D9FE7,0x07ED0870,0x20883C9C,0xF3D2FCA2,0xFDABEB32,
0x1A2304E1,0xF16BFF87,0x25AE3319,0xE878D70A,0xD490C154,0x38EC12AF,0xF91F31A3,0xE0AED28B,
0x02C6128E,0xFEDCFC6B,0xFDCBE6EA,0xBF2DE553,0x48391B1F,0xD6ABE832,0xE65AC56B,0x1037F600,
0xF2E42F0B,0xD62FE3A5,0xF2960B3C,0xFAF7E701,0x2F5032E2,0x1B5D03A0,0xFB7F0CBF,0x1FBC1308,
0x95EDFCA7,0x2102006B,0x2C3DF25B,0xF4A70B5A,0x0A781F9C,0x040703AD,0xED260CC6,0xF731CD46,
0xDA85FC51,0x4AB544AD,0xCCE116C4,0x293AF078,0xFB8DEE08,0x2CFF135B,0xD653E8EF,0xFEA11AF3,
0xE20A0141,0xFE2E1650,0x1B8C0346,0xC793F432,0xFC4CB572,0x0AA632BA,0xEAF9CC99,0x03FE37AB,
0xFF8DED26,0x0C294A3A,0xDF9FC0DA,0x50201A84,0x25FB0718,0xFEE0F1BE,0xEED5E184,0xF549E895,
0x1CFB1DBC,0xE45AF77C,0x186B024F,0xDF31E91F,0xE03EED82,0xCB62D21E,0x2AB91B46,0x1FC14AF5,
0xE653E9B7,0x18861346,0xF7391650,0xFF7AF413,0x0E4D1015,0xFEA501B2,0xE8DEF59F,0x13EAF967,
0x090C0618,0x085C0490,0xCBA6CF3E,0x560C0C22,0xF7F84BB7,0xE340D1F6,0x1A081F91,0x038904FE,
0xFAD81450,0x151AFB80,0x02DEEE36,0xC6B5E412,0xEAF6B3D1,0x1A7720AD,0xE0CCDBE3,0x30901A30,
0x2C730279,0x02FDF6EB,0x025B1C85,0xFD26F4AD,0x008CF8F1,0x17350E8A,0x02C40B69,0xF410284E,
0x0A1DE5B0,0x1E2D1DF7,0xF2EF0AB3,0x9DF3AF6F,0x3ECE446A,0xAB46E5B2,0xF1F9A3D8,0x1AAA12EB,
0xC95AE54C,0xFFFBFAD6,0x199FFD72,0xF1161F92,0xF676C968,0x0C40390D,0x09F51E7A,0xD8112273,
0x0EF4F941,0x12F30783,0xFCF118E9,0xB51BBA30,0xFD0D0BDE,0xFFD4F8F9,0x28233CD2,0x1A210254,
0xB9EAD424,0x096FCA04,0x305740D5,0x26FD1E7F,0xFC3F388C,0xF60A07F4,0x12E4D7C7,0xF4D218D5,
0xFDD4083A,0xD5F1E566,0x15EBF5DA,0xD07CD752,0x1898E889,0x057C125E,0xB4C9079A,0x046ECF79,
0x344D1FBC,0xED9B1E08,0x03F500E2,0xF8C7EDFB,0x56E22E1D,0x0F5F2363,0xB431FEA9,0x0452DBBA,
0x0CF324F5,0x0DDB0868,0xF5ACE117,0x132727E6,0xF9B9168C,0xEA36E591,0xB902D871,0x22B6FCF7,
0xD4ACF4E1,0x54FA04EA,0xF582FA9C,0xB2D4DD2E,0x1D750467,0x34CD201D,0xD37D1AF2,0x1B9AE742,
0xCB533894,0x29610783,0x128CDE18,0x00750A3A,0xE61BF248,0x1369F89F,0x1CD33397,0xF7DCEB14,
0x13991F19,0x064E0160,0xC92D22F0,0x1262D2B7,0x0F060ED7,0xFE3FE718,0x102203ED,0xEFE3FB32,
0xC781CFFD,0x12AC08CA,0xDDE7EC9D,0x1D060883,0x1AECDCBB,0xCD010E52,0x157427E6,0xE740E680,
0x266405D2,0x09AE01D3,0xC3A1F1A9,0x4D8F2AD1,0x052724C3,0xFE99EEC5,0xB1E8F0FE,0x443BBEE4,
0xDC7C4074,0xE0AAB49C,0xE9142BD7,0x19E80C38,0xF6C748F8,0x1DAC0436,0xFEA50FAC,0x0680D111,
0xE6FD1151,0x4216A350,0xCF791636,0xEDC4FEB1,0x2373231D,0xABC0BD6E,0x0F570046,0x201F1CDA,
0x3AE81322,0xBE0802F0,0x53D1EBAE,0x15E02ADB,0xF847D1D4,0x27ABDE96,0xE0481F5D,0x2544F6AD,
0xED920511,0x18B1DF73,0xD6CD0E31,0x3471C82D,0xD35432B3,0xF3EFEE9F,0xE0C9237C,0xF7521779,
0x3B47DFBC,0xD9BA136D,0xF61B08BB,0x2FA80469,0xB981D6EB,0x1882E90F,0x0E8617D0,0x0FB640CB,
0xFBDABC26,0xF90AE402,0xFB2EEC93,0x1EB40E68,0x03C908A2,0x30181FA1,0xE5B91281,0x064AFCB6,
0xE7E9051B,0x0292E4F8,0x1E661783,0xDFF4EE7C,0xD8F2EB7C,0xF2CFB8D9,0x17FA045A,0x0B96FD6B,
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
};
