ghztomash/callisto-module/firmware/drum-synth/AudioSampleKick.cpp

// Audio data converted from WAV file by wav2sketch

#include "AudioSampleKick.h"

// Converted from Kick.wav, using 44100 Hz, 16 bit PCM encoding
const unsigned int AudioSampleKick[11841] = {
0x81005C5C,0x00000000,0x00010000,0x00080003,0x00150010,0x000D0014,0xFFF40001,0xFFD3FFE4,
0xFFACFFC0,0xFF86FF9A,0xFF62FF73,0xFF43FF52,0xFF25FF34,0xFEFFFF0F,0xFEEAFEF1,0xFEE2FEE7,
0xFED3FEDE,0xFECFFED3,0xFEE7FEDA,0xFEE3FEE1,0xFEEEFEEF,0xFF03FEF5,0xFF05FEF6,0xFF58FF34,
0xFF62FF6B,0xFF73FF62,0xFF86FF70,0xFFD5FFAB,0xFFE7FFD7,0xFFFD0005,0x0020001D,0x005D0049,
0x00990066,0x014600DA,0x015B0167,0x019B015D,0x01C60183,0x01EC01F7,0x02AD020F,0x02EA02B9,
0x040B0355,0x050204A0,0x0531050E,0x05A205A7,0x05930565,0x065E05C6,0x06E706CD,0x076D0717,
0x0A1D081E,0x0DF30BF4,0x11EC0FBD,0x1725149B,0x1D781A52,0x23E320CC,0x2AB7277E,0x321B2E4E,
0x4E423A9E,0x78D667FF,0x742B7B95,0x665A6AC2,0x6D3867EF,0x79D17430,0x7B417BB4,0x796D7A0E,
0x7A4279AE,0x7E847CA2,0x7FCF7F93,0x7F837F7C,0x7F607FAF,0x7F737EF1,0x7F8C7FDF,0x7FDB7FCC,
0x7F927FFF,0x7FA37F48,0x7E5C7F1D,0x7C8D7D6E,0x7B237BED,0x7AAB7AD6,0x798C7A29,0x75307796,
0x72B673E4,0x6F6C7127,0x6A1E6CBE,0x662E67D7,0x626C6447,0x5B515FC1,0x542F57DD,0x4AD74F96,
0x422845DD,0x3AE33EF6,0x30CA35CD,0x280F2CB7,0x1E5D22CC,0x152119A8,0x0C4F1090,0x046F088A,
0xFC6B0066,0xF4FEF8D8,0xED1EF0EF,0xE585E939,0xDD8DE18E,0xD827DA9F,0xD20FD52A,0xCA31CDF4,
0xC2D8C6E0,0xBD28BF83,0xB96BBB37,0xB4C1B6EF,0xB027B27D,0xAB81AD47,0xA8AFA9FC,0xA632A770,
0xA40EA51D,0xA11DA28F,0x9E5E9FAF,0x9CB79D78,0x9BB79C40,0x9B619BF4,0x9A009AAB,0x98609976,
0x980B97EE,0x98979803,0x99C09954,0x9C429AC8,0x9E399D53,0x9F2B9EAA,0xA0F9A062,0xA23FA16E,
0xA356A33F,0xA4BDA396,0xA62FA548,0xA80BA6D7,0xAACEA979,0xAD6FAC11,0xB074AF2A,0xB3FEB1CE,
0xB863B5C5,0xBCFABA8D,0xC2FDC00D,0xC812C59D,0xCDE3CA66,0xD3F8D0E5,0xDB2CD79D,0xE0BDDDE5,
0xE95BE577,0xF030ED1E,0xF7A8F3C7,0xFE71FB59,0x043F01A8,0x0A1B0708,0x12900E9A,0x1A3616B0,
0x21801DC1,0x291B257A,0x2FE42C91,0x35D632CE,0x3D34399C,0x450A4137,0x4C3648D0,0x526F4FA8,
0x57F65512,0x5DA45AFF,0x61BE5FD1,0x65EB6391,0x690B67D5,0x6C556A25,0x6FDB6E56,0x711570CC,
0x731671F2,0x74D17381,0x76CC760A,0x77AE76FF,0x77CB77C7,0x787A77E9,0x79617949,0x7AA679F2,
0x7AA47AE2,0x7B297A91,0x7B007B69,0x791B7975,0x7853790C,0x761E7709,0x74587538,0x723372FC,
0x6F9370EB,0x6D876E9E,0x6ACB6BCD,0x68CB69D4,0x65AF672D,0x63596455,0x60C961CA,0x5D635F5C,
0x59235B3C,0x54A956AD,0x501D52B0,0x495F4CAF,0x42E8466E,0x3BBD3F60,0x34FC387B,0x2DF7315A,
0x270F2AEA,0x200C236D,0x19181CDE,0x12DA163B,0x0C300F7B,0x06770975,0x00380356,0xFA8FFD48,
0xF5CEF7F2,0xF085F339,0xEACBEDB0,0xE67EE86B,0xE095E3C8,0xDB4CDD85,0xD5BFD8CC,0xD0EED322,
0xCC00CEFA,0xC755C9A2,0xC208C480,0xBDC0BF9B,0xBA21BC0A,0xB5A2B7C3,0xB20DB455,0xAF12B05D,
0xAC6FADC3,0xA935AA9E,0xA6ACA7E3,0xA3C8A54D,0xA1BEA2B5,0x9FBDA091,0x9E069ED5,0x9C969D53,
0x9BC59C2C,0x9B899BD9,0x9B599B83,0x9B4F9B57,0x9A6F9AA6,0x9A559A3B,0x9B079AC0,0x9A729AE2,
0x9B449B08,0x9AEA9B1A,0x9BCD9AFE,0x9CD39CA2,0x9D629D0B,0x9DB89DCF,0x9ECB9E35,0x9EF99ED7,
0x9F2E9F2C,0xA0109FB0,0xA115A0B8,0xA182A0E7,0xA376A2C1,0xA519A43F,0xA6BCA5C5,0xA8CBA7BA,
0xAAC0A9B5,0xADB5AC4A,0xB048AEAA,0xB221B13F,0xB459B319,0xB78DB613,0xBBA9B947,0xBFDCBDFC,
0xC42CC1EB,0xC792C5E9,0xCCFACA1F,0xD1ABCF68,0xD5ABD3BB,0xD9C9D7A6,0xDEFDDBF6,0xE473E1AB,
0xE960E720,0xEEDDEBDE,0xF34DF0A1,0xF7BEF58B,0xFCE6FA43,0x017CFF3A,0x07140459,0x0C2D0991,
0x11520ECE,0x161813E3,0x1AF418C0,0x20011D1C,0x259922CC,0x2B2B2841,0x30212DB8,0x35AE32C2,
0x3B4B385C,0x40413E24,0x458F42A8,0x4A2A47EF,0x4EDA4C6F,0x53495102,0x580E55DE,0x5C245A1E,
0x5EE35DA0,0x622C6086,0x64F063A5,0x6724661A,0x68C66805,0x6AF869AC,0x6CAD6BF2,0x6DF76D5A,
0x6F6F6EBA,0x70ED7049,0x728F71A0,0x731672CD,0x73EC7356,0x74E17465,0x75F27586,0x771D7667,
0x77887740,0x786777CD,0x78C478BB,0x793978F7,0x796D7965,0x78EC797A,0x78AC788E,0x77F97874,
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
};
