ghztomash/callisto-module/firmware/drum-synth/AudioSampleSnare1.cpp

// Audio data converted from WAV file by wav2sketch

#include "AudioSampleSnare1.h"

// Converted from snare1.wav, using 44100 Hz, 16 bit PCM encoding
const unsigned int AudioSampleSnare1[2817] = {
0x81001589,0x00010000,0xFFFF0009,0xFFB4FFCF,0x002CFFDE,0x00AB006A,0x003500B8,0xFEF0FF66,
0xFF3AFED3,0x009C004D,0xFE88FF94,0xFE03FE1D,0xFDF7FE02,0xFDD4FDE6,0xFDB9FDC3,0xFDABFDAE,
0xFDA4FDA4,0xFD9DFDA0,0xFD73FD8B,0xFD47FD5D,0xFD2BFD3C,0xFD1BFD27,0xFD14FD1A,0xFD15FD15,
0xFD1EFD17,0xFD29FD1F,0xFD1EFD1F,0xFD11FD0E,0xFD0EFD08,0xFD11FD0D,0xFD1EFD17,0x0251FD54,
0x0EFB0D77,0x000804F1,0x0EE204FF,0x1C471896,0xFE1D0FC8,0x0ED0FF0D,0x11231A08,0xFA35FCEE,
0x18B00AB8,0x1A601C42,0x158E178E,0x11F2143C,0x0EC30F10,0x0F3E0F94,0x0CFB0E3A,0x0ACB0BD6,
0x08E509D6,0x071C07FF,0x056B0643,0x03DC04A4,0x0272032A,0x012A01D6,0xFFF800AB,0xFEDFFFB9,
0xF08AF6C4,0xFC88F57B,0xFF8DFFA8,0xFDBDFE99,0xFD08FD5A,0xFC92FCE1,0xFC16FC6F,0xFB95FC1B,
0xFA60FC0E,0xDAD1E965,0xCF0ED2EA,0xFB7AE207,0x0600070D,0xD3F0F7A2,0xDCEDC06A,0x07B4022B,
0xD9D5EA7A,0xEDF4E902,0xDEB7DF18,0xE9C6EA83,0xD221E1E8,0xC335C048,0x1542E829,0xF35219C5,
0xE561D883,0xDFBDEF41,0xF503D65D,0x1EB220DC,0xDA3EF83D,0xEBFDD36F,0x207714C0,0xEF220A8F,
0xF3F3E5D7,0x00B8040D,0xEB23F1DD,0xEFDBEBC8,0xF61CF349,0x126FFDDB,0x1EAA24D5,0x0B951416,
0xFB4500D6,0x11F7FFA0,0x0F9E1AFF,0x004F036D,0x2EC212A5,0x0FE92AE1,0xFBE3FF45,0x0160FE8A,
0x03C20308,0x04D7044D,0x060E0576,0x0720069D,0x07FF078D,0x08B3084C,0x093F08DF,0x09A7094B,
0x09F5098F,0x0A4E099D,0x0B61094A,0x2AD321DB,0x078C1792,0x08430278,0x096C0CAA,0x0362053A,
0x03940375,0x10FF05E5,0x213C21DF,0xFFC90F56,0x08ECFFB3,0x01820A38,0x30AF044A,0x437E5962,
0xF6430F79,0x0FF9FDDF,0x375A2729,0x447D4421,0x1813265A,0x398B28DC,0x0DE02FBD,0x1C9F0623,
0x28262ACA,0x1C441F60,0x07621A59,0xF893F2E3,0x0FB5092B,0x02BD0A40,0x024501BF,0xFEEE0145,
0xFA05FC61,0xF61BF7EC,0xF2C8F451,0xEFEBF136,0xED87EE99,0xEB93EC76,0xEA0BEAC3,0xE8E4E975,
0xE818E882,0xE7A1E7E3,0xE774E78E,0xE78AE77C,0xE7D8E7A6,0xE858E807,0xE902E899,0xE9CBE954,
0xEAB2EA32,0xEBB3EB2F,0xECC5EC41,0xEDE7ED62,0xEF17EE8E,0xF04EEFC0,0xF189F0F3,0xF2C5F225,
0xF3FCF357,0xF529F483,0xF64AF5AC,0xF758F6D6,0xF846F801,0xEA37F166,0xF9DAF057,0xFE76FDF5,
0xF175FCA8,0xDA96DEAD,0xFEDCED1D,0xC7CAF0F7,0xBF31AC15,0xFE7AEC2C,0xE143F2A6,0xDB24D36C,
0xDF50EACC,0xBF3BC688,0xD7C3CD22,0xD49ED5B0,0xDC1AD740,0xE5F4E145,0xF0FBEB74,0xFC36F69A,
0xFBB0FD4B,0xFF8EFD20,0x09D20326,0x0CA40DE9,0x0CDE0BEB,0x10B50EDA,0x13A3127B,0x1ADD1543,
0x19211C30,0x183017FC,0x19C11912,0x1A861A44,0x1ADA1ABF,0x1AED1AF1,0x1ABE1AE0,0x1A541A8F,
0x19B61A07,0x18ED194E,0x17FE186F,0x16EE176E,0x15C61653,0x14891525,0x133E13E7,0x11E912A0,
0x10911151,0x0F390FFE,0x0DE30EA9,0x0C670D55,0x1DF71233,0x0DC61AF8,0x04780671,0x052A04D8,
0x047D04F4,0x037803E9,0x029E0300,0x22100783,0x4BFC4920,0x06CD26C6,0xF8C1FC80,0xF04FF3DA,
0x0948F473,0x28D22025,0x044E1C0C,0x0FCB016B,0xFF15119F,0x1071F9D9,0x0FFE1F02,0x04B3FB4C,
0x2C7D1D8A,0x3A9036A3,0x301037CF,0x06D51FF1,0xD6D5EA4A,0xFD7BDC3D,0x1D4E1C96,0xD378FAF1,
0xFA7BD839,0x11440F11,0x05440B89,0x091D036B,0x00880A97,0xF047F47B,0x032BF8B4,0xFDC505D3,
0xDC4AE8DD,0xF8CEE78F,0xE34AF8CB,0xDF68D529,0xF9BEEEE7,0xFFC8FFB4,0xFC28FE16,0xFA0AFB15,
0xF5ECF9A5,0xE71EEA1A,0xF7AAF052,0xF3DBF97F,0xD6DDE3C9,0xF541E21E,0xF702FC9F,0xEA5FEB09,
0xFB62F430,0xE342F21E,0xF7A6E8B4,0xFF7DFF80,0xEED3F73A,0xEEC7EB91,0x00B1F8E6,0xF54EFF7D,
0xEB19ECF3,0xF42DEB61,0xFEC0FFA6,0xFC57F8CF,0x0670040A,0xF515FEAF,0x0376F98A,0x06130896,
0xF910FBD9,0x05E20151,0xC4A3F04E,0xDEBAB8C5,0x186B07EA,0xFFB2145A,0xFC40F156,0x11BA0DB6,
0xED3201AE,0xFD85EC51,0x04AD0AD3,0xEC65F55D,0x0685F43B,0x18E6129B,0x16051AC9,0xE86C0648,
0xCBA4CE48,0x0B6EE562,0x247B22BF,0xD9F306B1,0xCDE6C7A4,0x0906E59C,0x2169218F,0xDF43059E,
0xEB81D3D3,0x0F71047C,0x1B151885,0xF9BE0E6A,0xDBB6E3B7,0xF213E5E3,0xF994F7C3,0x15FA0461,
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
};
